theArnoll/Charge_Limitation_Switch/Schematic.kicad_sch

## KiCad design Schematic.kicad_sch (2026-01-19)

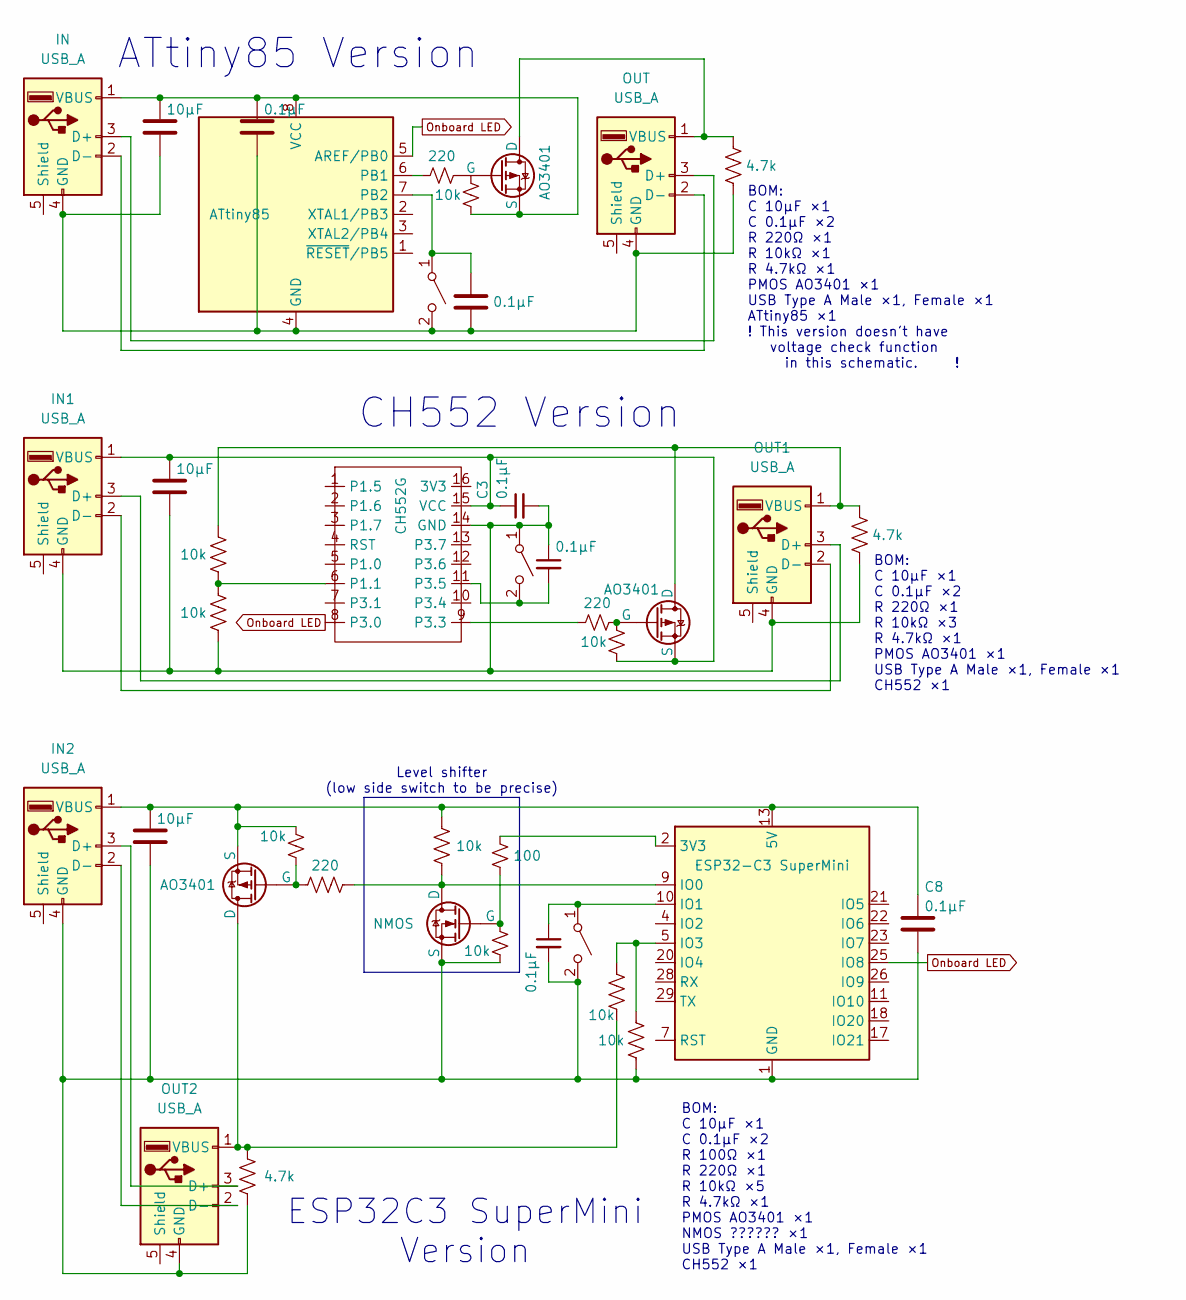
[picture p2: schematic Schematic.kicad_sch]

Parts:
C1, C2, C3, C6, C8, C9: 0.1μF
C4, C5, C7: 10μF
IN, IN1, IN2: USB_A
OUT, OUT1, OUT2: USB_A
PMOS, PMOS1, PMOS2: AO3401
Q1: NMOS
R1, R3, R7: 220
R2, R4, R8, R10, R12, R13, R14, R15, R16: 10k
R5, R6, R9: 4.7k
R11: 100
SW1, SW2, SW3: SW_SPST
U1: ATtiny85; SOIC-8_5.3x5.3mm_P1.27mm
U2: CH552G
U4: ESP32-C3 SuperMini; ESP32-C3-DevKitM-1

Connections:
unnamed: C1.1, C3.2, C4.2, IN1.4 (GND), OUT1.4 (GND), R5.2, R14.2, SW2.1 (A), U2.14 (GND)
unnamed: C1.2, SW2.2 (B), U2.11 (P3.5)
unnamed: C2.1, SW1.1 (A), U1.7 (PB2)
unnamed: C2.2, C5.2, C6.2, IN.4 (GND), OUT.4 (GND), R6.2, SW1.2 (B), U1.4 (GND)
unnamed: C3.1, C4.1, IN1.1 (VBUS), PMOS1.3 (S), R4.2, U2.15 (VCC)
unnamed: C5.1, C6.1, IN.1 (VBUS), PMOS.3 (S), R2.2, U1.8 (VCC)
unnamed: C7.1, C8.1, IN2.1 (VBUS), PMOS2.3 (S), R8.1, R10.1, U4.13 (5V), U4.14 (5V)
unnamed: C7.2, C8.2, C9.2, IN2.4 (GND), OUT2.4 (GND), Q1.3 (S), R9.2, R13.2, R16.2, SW3.2 (B), U4.1 (GND), U4.6 (GND), U4.8 (GND), U4.12 (GND), U4.15 (GND), U4.16 (GND), U4.19 (GND), U4.24 (GND), U4.27 (GND), U4.30 (GND)
unnamed: C9.1, SW3.1 (A), U4.10 (IO1)
unnamed: IN1.2 (D-), OUT1.2 (D-)
unnamed: IN1.3 (D+), OUT1.3 (D+)
unnamed: IN2.2 (D-), OUT2.2 (D-)
unnamed: IN2.3 (D+), OUT2.3 (D+)
unnamed: IN.2 (D-), OUT.2 (D-)
unnamed: IN.3 (D+), OUT.3 (D+)
unnamed: OUT1.1 (VBUS), PMOS1.1 (D), R5.1, R12.1
unnamed: OUT2.1 (VBUS), PMOS2.1 (D), R9.1, R15.2
unnamed: OUT.1 (VBUS), PMOS.1 (D), R6.1
unnamed: PMOS1.2 (G), R3.2, R4.1
unnamed: PMOS2.2 (G), R7.1, R8.2
unnamed: PMOS.2 (G), R1.2
unnamed: Q1.1 (D), R7.2, R10.2, U4.9 (IO0)
unnamed: Q1.2 (G), R11.2, R13.1
unnamed: R1.1, U1.6 (PB1)
unnamed: R3.1, U2.9 (P3.3)
unnamed: R11.1, U4.2 (3V3), U4.3 (3V3)
unnamed: R12.2, R14.1, U2.6 (P1.1)
unnamed: R15.1, R16.1, U4.5 (IO3)
Onboard LED: U1.5 (AREF/PB0), U2.8 (P3.0), U4.25 (IO8)

Notes on the sheet:
ATtiny85 Version
BOM: C 10μF ×1 C 0.1μF ×2 R 220Ω ×1 R 10kΩ ×1 R 4.7kΩ ×1 PMOS AO3401 ×1 USB Type A Male ×1, Female ×1 ATtiny85 ×1 ! This version doesn't have voltage check function in this schematic. !
CH552 Version
Level shifter (low side switch to be precise)
BOM: C 10μF ×1 C 0.1μF ×2 R 100Ω ×1 R 220Ω ×1 R 10kΩ ×5 R 4.7kΩ ×1 PMOS AO3401 ×1 NMOS ?????? ×1 USB Type A Male ×1, Female ×1 CH552 ×1
ESP32C3 SuperMini Version
BOM: C 10μF ×1 C 0.1μF ×2 R 220Ω ×1 R 10kΩ ×3 R 4.7kΩ ×1 PMOS AO3401 ×1 USB Type A Male ×1, Female ×1 CH552 ×1
